bill-orange/Sprinkler_Controller/data/wait_for_it.png

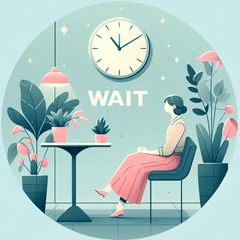
data/wait_for_it.png
