bill-orange/Sprinkler_Controller/data/11.png

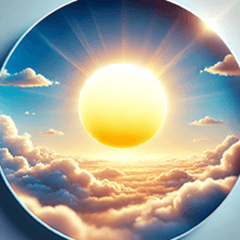
data/11.png
