bill-orange/Sprinkler_Controller/data/12.png

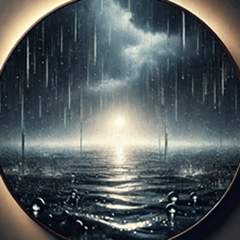
data/12.png
