bill-orange/Sprinkler_Controller/data/AI_computer_eye.png

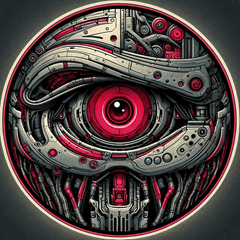
data/AI_computer_eye.png
