bill-orange/Sprinkler_Controller/data/Alternate_error_graphic.png

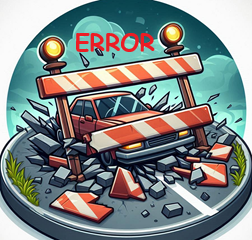
data/Alternate_error_graphic.png
