bill-orange/Sprinkler_Controller/data/confused_AI.png

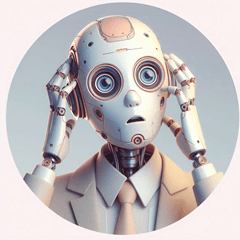
data/confused_AI.png
