bill-orange/Sprinkler_Controller/data/SD_No.png

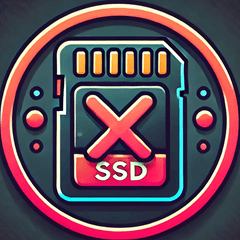
data/SD_No.png
