bill-orange/Sprinkler_Controller/data/SD_Yes.png

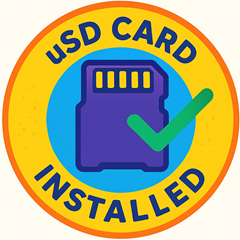
data/SD_Yes.png
