bill-orange/Sprinkler_Controller/data/WIP.png

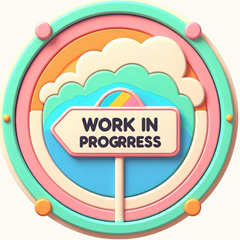
data/WIP.png
